mkdl/Unix60/Pictures/8.jpg

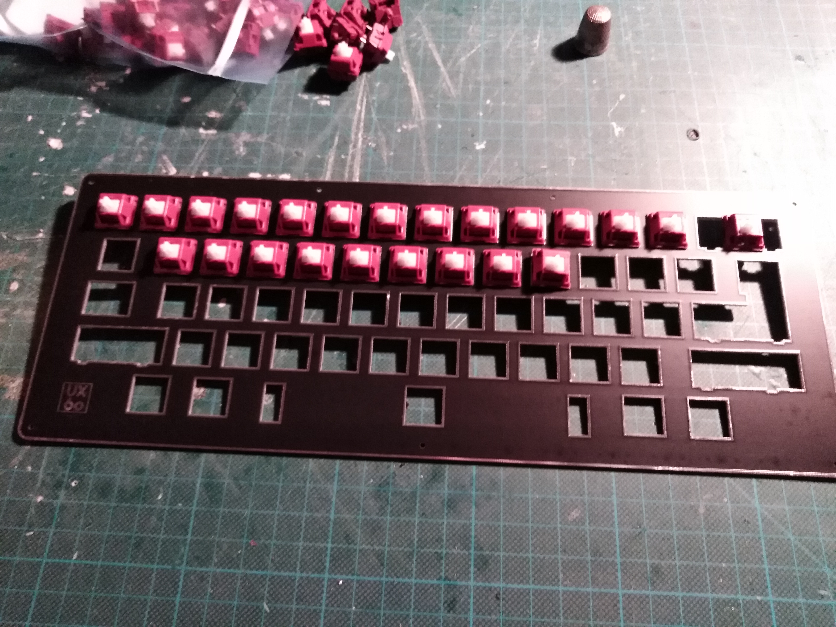
Pictures/8.jpg
